MX55554Te/AquaDose/docs/assets/3d-model/images/case_01.png

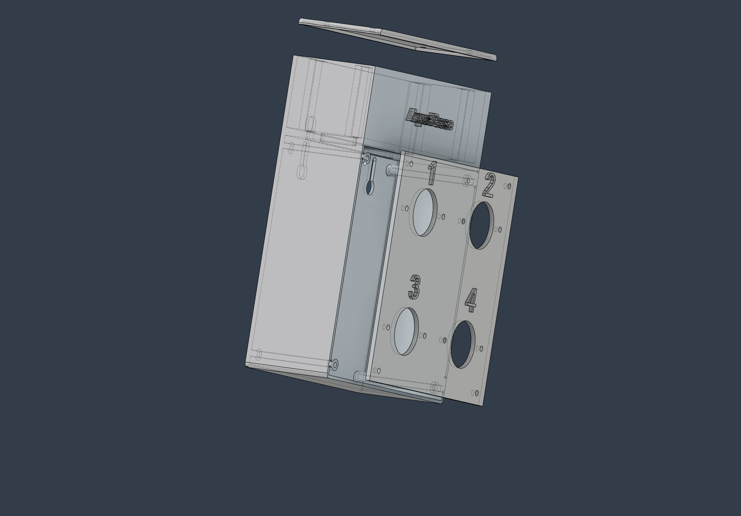
docs/assets/3d-model/images/case_01.png
