MX55554Te/AquaDose/docs/assets/3d-model/images/case_04.png

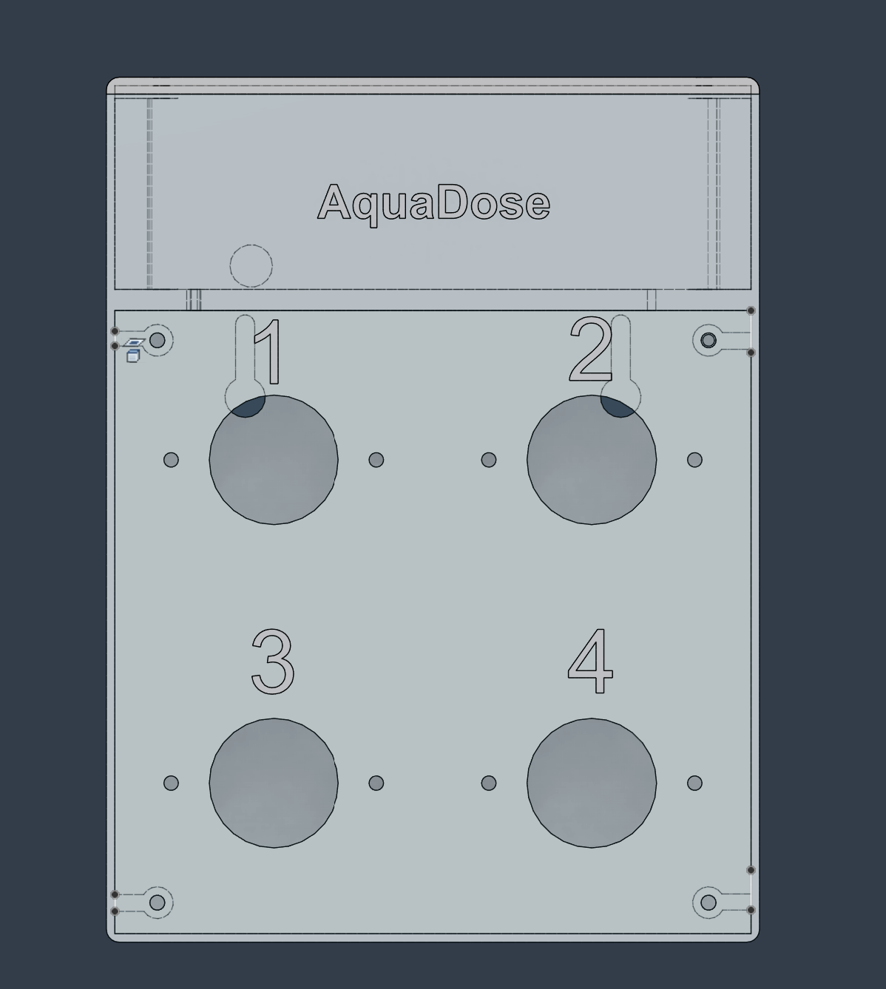
docs/assets/3d-model/images/case_04.png
