MX55554Te/AquaDose/docs/assets/screenshots/04-pump-actions.png

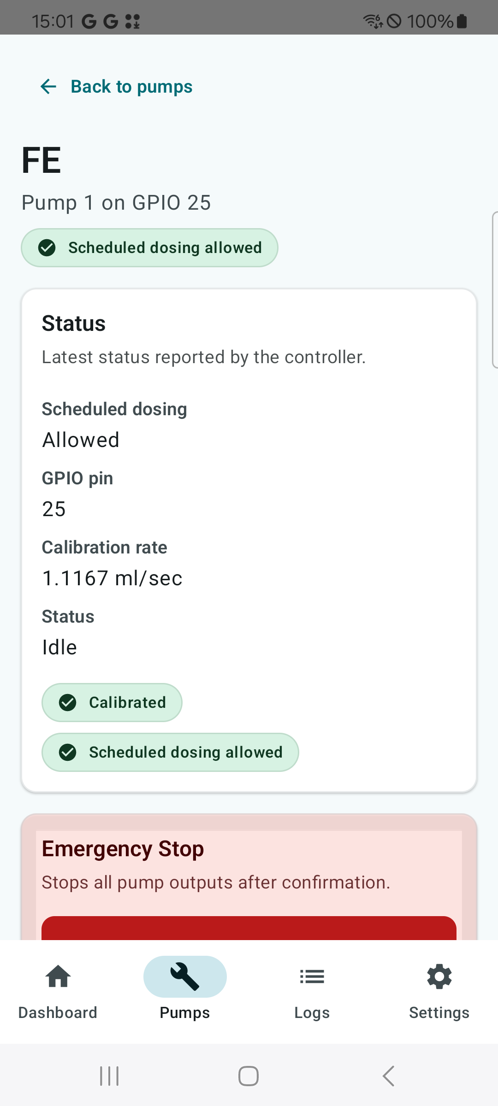
docs/assets/screenshots/04-pump-actions.png
