MX55554Te/AquaDose/docs/assets/screenshots/07-schedule-screen.png

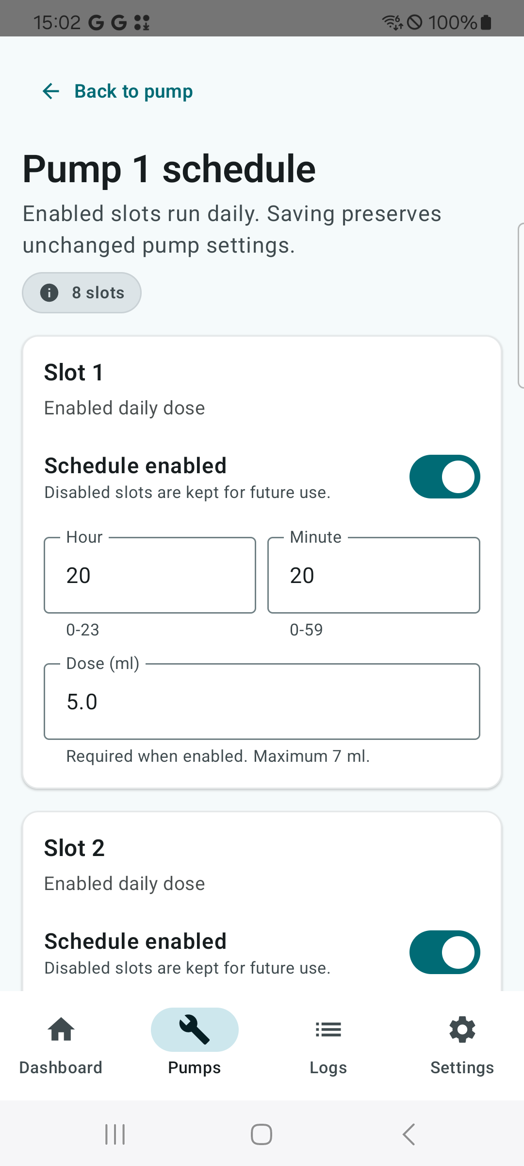
docs/assets/screenshots/07-schedule-screen.png
