MX55554Te/AquaDose/docs/assets/screenshots/10-factory-reset-flow.png

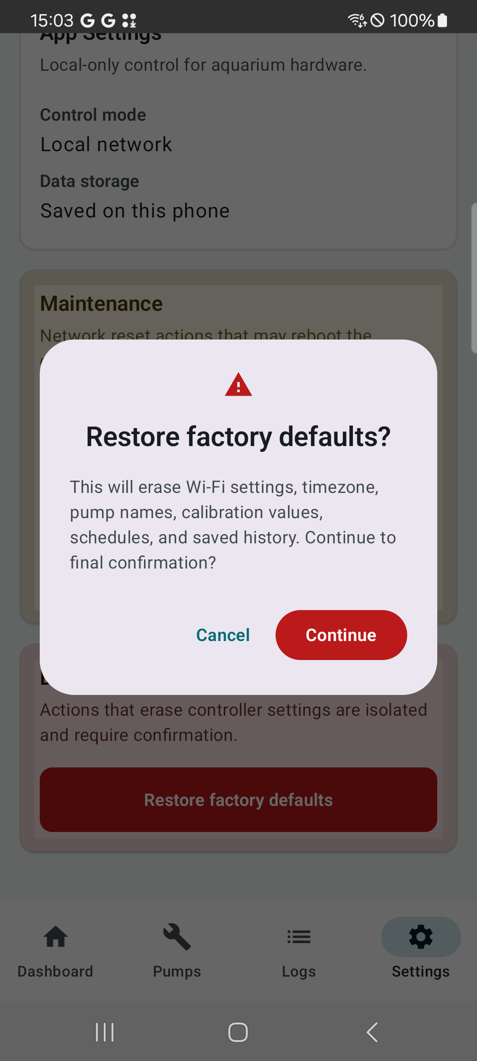
docs/assets/screenshots/10-factory-reset-flow.png
