MX55554Te/AquaDose/docs/assets/screenshots/11-factory-reset-confirmation.png

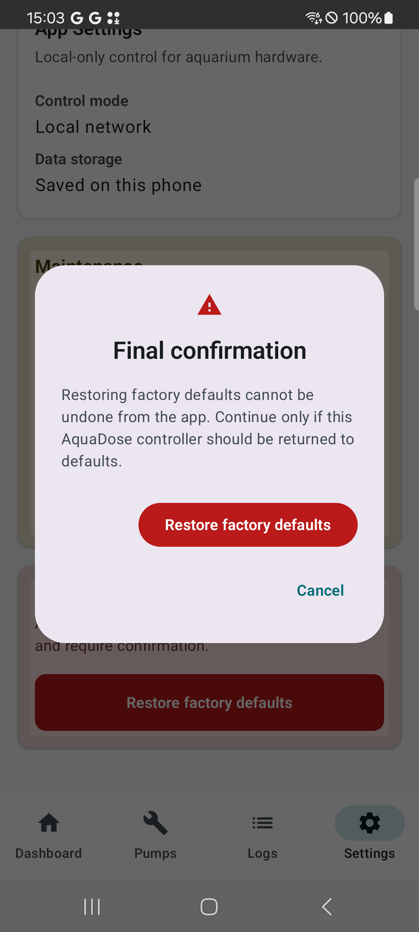
docs/assets/screenshots/11-factory-reset-confirmation.png
