MX55554Te/AquaDose/docs/assets/screenshots/05-calibration-screen.png

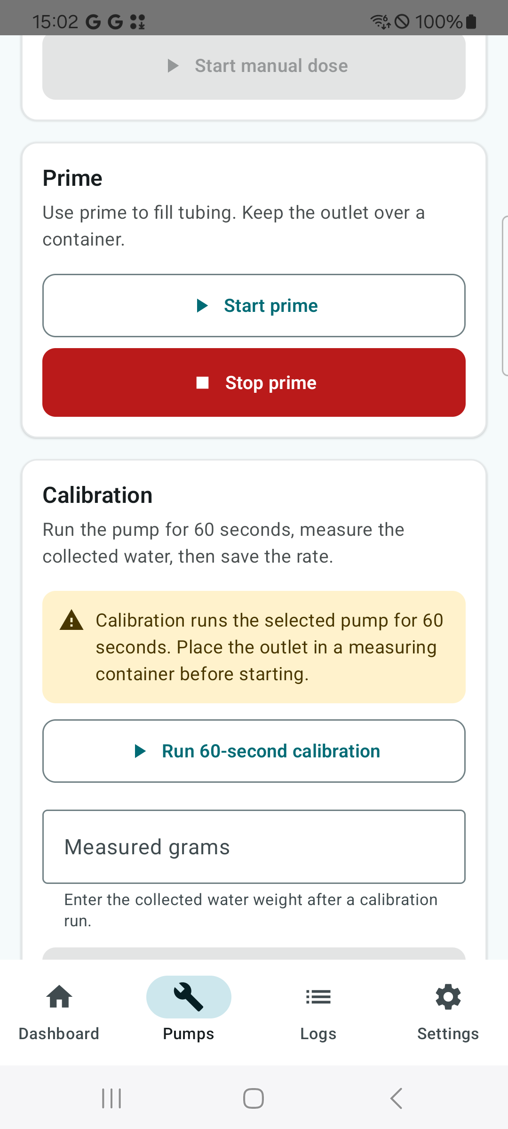
docs/assets/screenshots/05-calibration-screen.png
