MX55554Te/AquaDose/docs/assets/screenshots/09-settings-maintenance.png

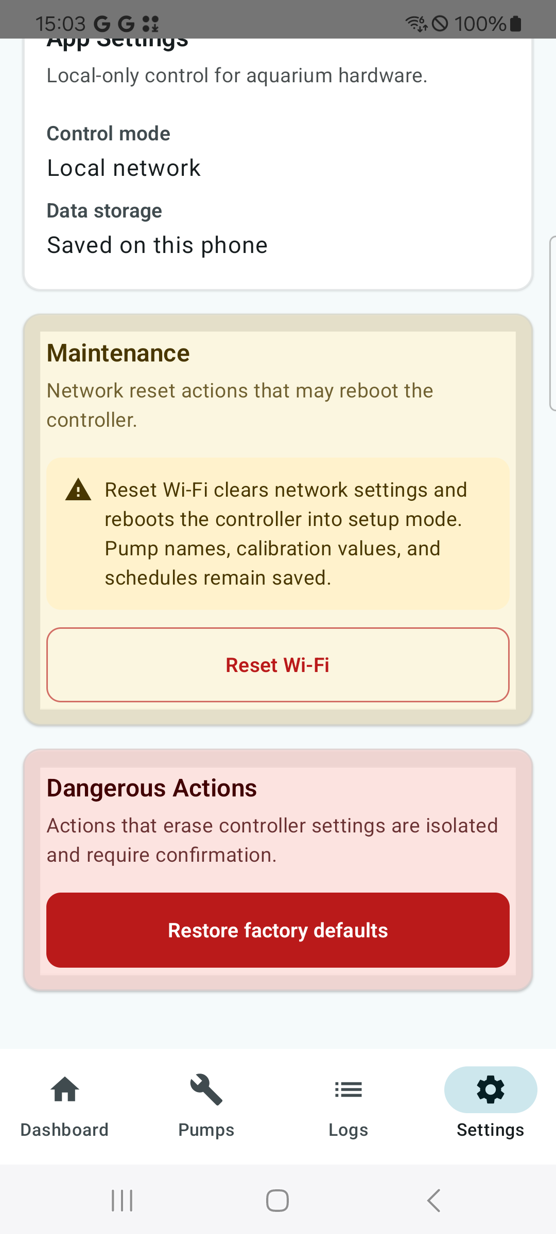
docs/assets/screenshots/09-settings-maintenance.png
